jordiorlando/EnLiST-Rover/Eagle/Rover Motor Controller/eagleUp/eagleUp_Rover Motor Controller_bottom_silk.png

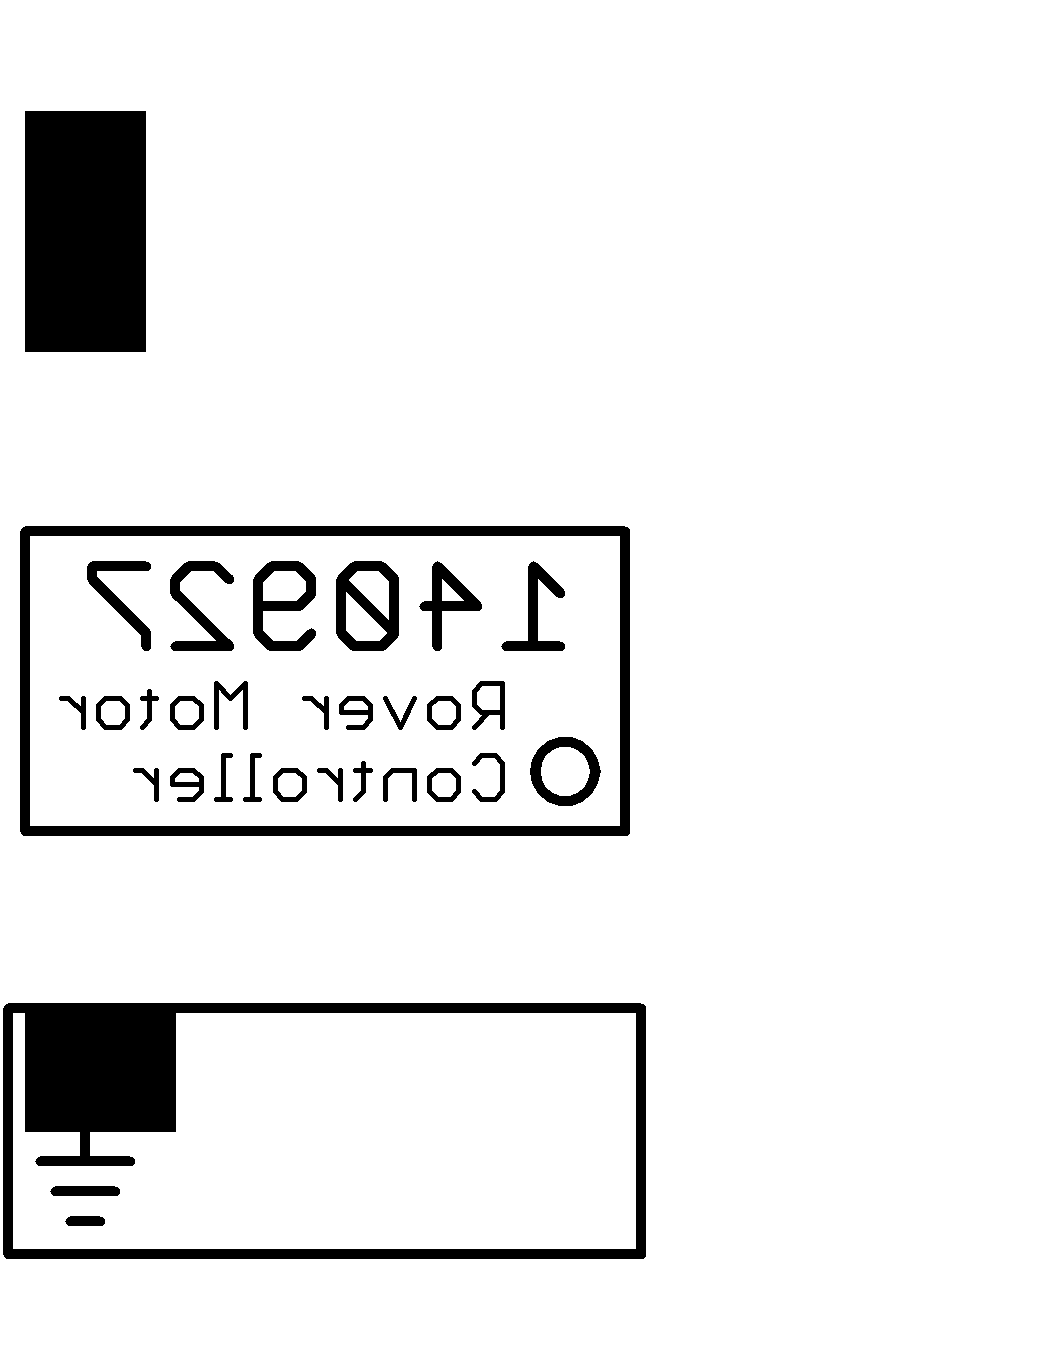
Eagle/Rover Motor Controller/eagleUp/eagleUp_Rover Motor Controller_bottom_silk.png
