jordiorlando/EnLiST-Rover/Eagle/Rover Motor Controller/eagleUp/eagleUp_Rover Motor Controller_outline.png

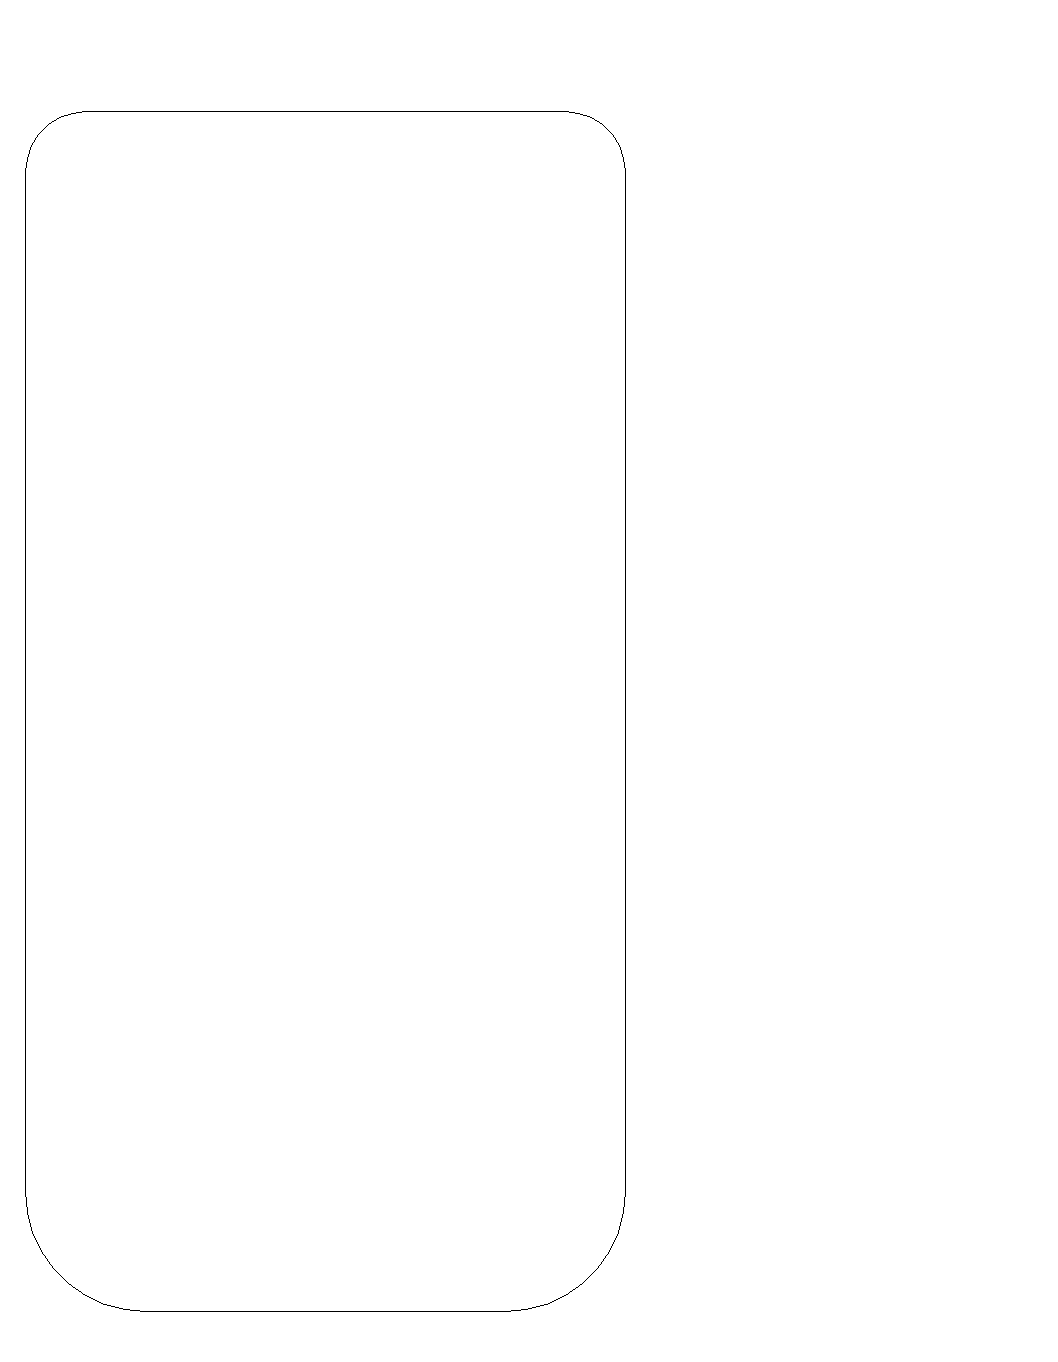
Eagle/Rover Motor Controller/eagleUp/eagleUp_Rover Motor Controller_outline.png
