jordiorlando/EnLiST-Rover/media/photos/15-01-04/IMG_0461.jpg

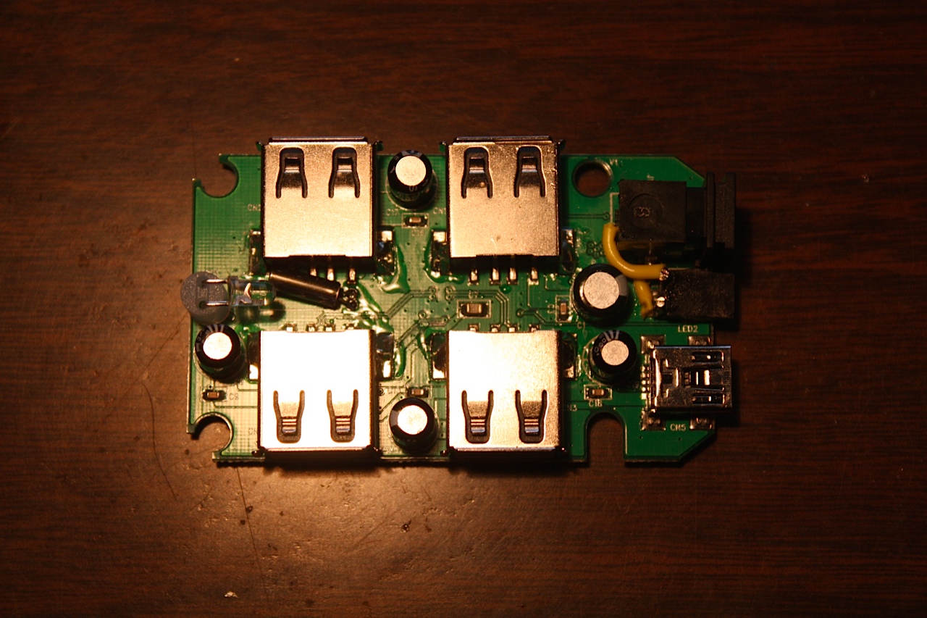
media/photos/15-01-04/IMG_0461.jpg
