jordiorlando/EnLiST-Rover/media/photos/15-01-04/IMG_0467.jpg

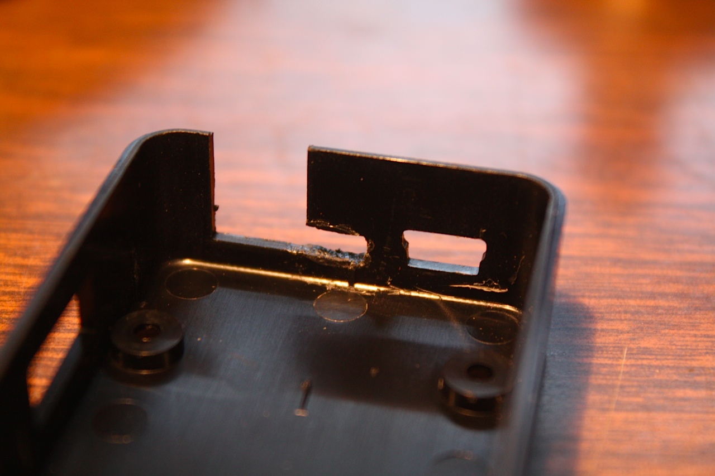
media/photos/15-01-04/IMG_0467.jpg
