jordiorlando/EnLiST-Rover/media/photos/15-01-04/IMG_0475.jpg

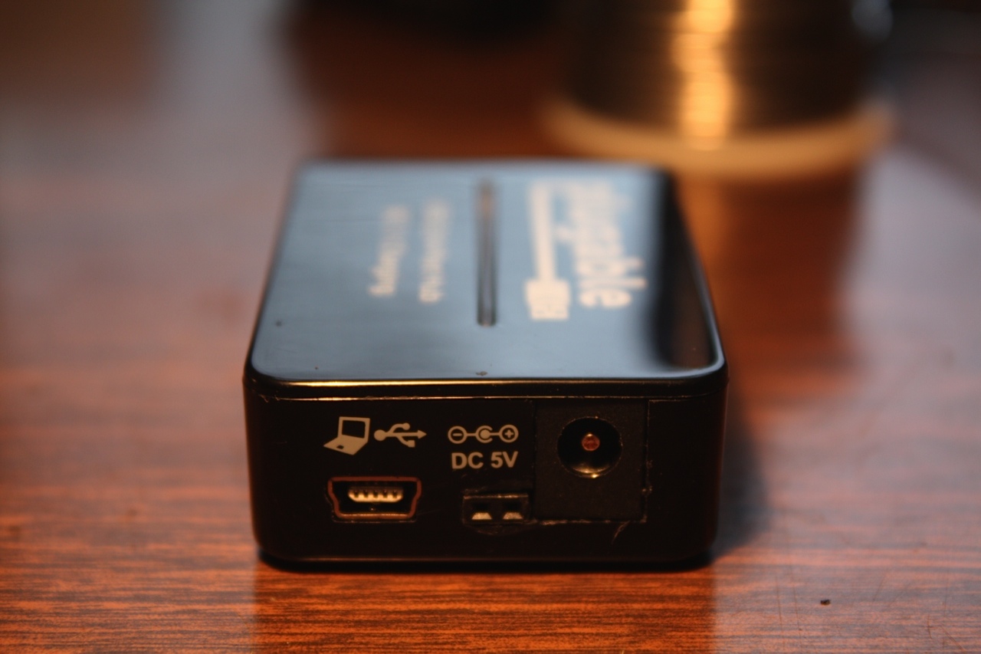
media/photos/15-01-04/IMG_0475.jpg
