jordiorlando/EnLiST-Rover/resources/hardware/Motor Controller Schematic.png

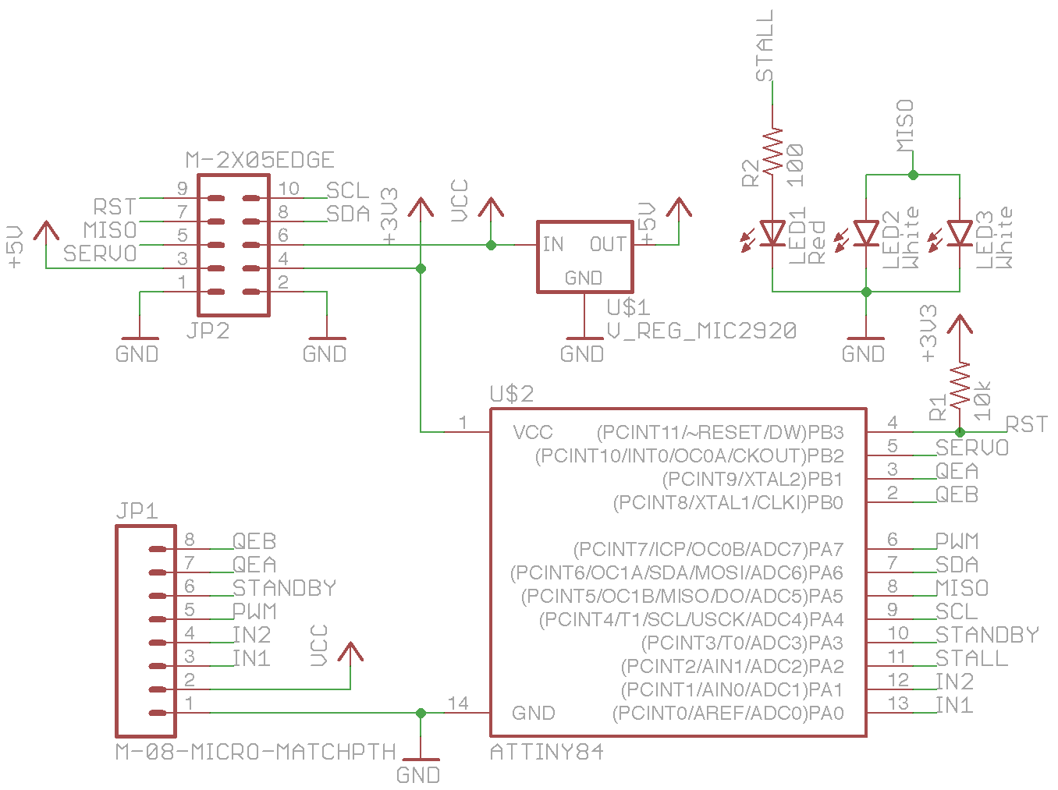
resources/hardware/Motor Controller Schematic.png
