jordiorlando/EnLiST-Rover/resources/Inspiration/Curiosity Rover.jpg

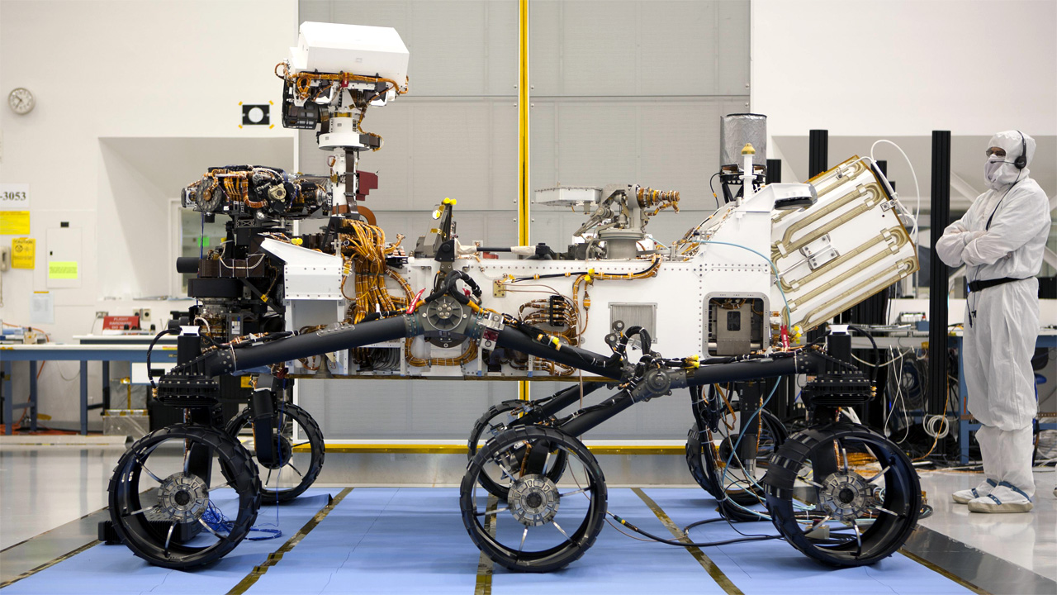
resources/Inspiration/Curiosity Rover.jpg
