jordiorlando/EnLiST-Rover/software/BBB/controllerInput.cpp

#include "controllerInput.h"

controllerInput::controllerInput(tcpSocket & server)
{
    this->server = &server;

    memset(&data, 0, sizeof(data));

    pfd.fd      = this->server->hostfd;
    pfd.events  = POLLIN;
    pfd.revents = 0;
}

void controllerInput::updateValues()
{
    //wait up to 100ms
    poll(&pfd, 1, 100);

    //data ready
    if (pfd.revents & POLLIN)
    {
        ssize_t len;
        unsigned char buf[6];

        //chew up any stale controller data
        while ((len = recv(pfd.fd, buf, 6, MSG_DONTWAIT)) > 0);

        data.square   = (buf[0] >> 0) & 0x1;
        data.cross    = (buf[0] >> 1) & 0x1;
        data.circle   = (buf[0] >> 2) & 0x1;
        data.triangle = (buf[0] >> 3) & 0x1;
        data.l1       = (buf[0] >> 4) & 0x1;
        data.l2       = (buf[0] >> 5) & 0x1;
        data.r1       = (buf[0] >> 6) & 0x1;
        data.r2       = (buf[0] >> 7) & 0x1;

        data.select      = (buf[1] >> 0) & 0x1;
        data.start       = (buf[1] >> 1) & 0x1;
        data.left_stick  = (buf[1] >> 2) & 0x1;
        data.right_stick = (buf[1] >> 3) & 0x1;
        data.d_up        = (buf[1] >> 4) & 0x1;
        data.d_down      = (buf[1] >> 5) & 0x1;
        data.d_left      = (buf[1] >> 6) & 0x1;
        data.d_right     = (buf[1] >> 7) & 0x1;

        data.left_x  = (float)( buf[2] - 0x80 + (1 * (buf[2] < 0x80)) ) / 0x80;
        data.left_y  = (float)( buf[3] - 0x80 + (1 * (buf[3] < 0x80)) ) / 0x80;
        data.right_x = (float)( buf[4] - 0x80 + (1 * (buf[4] < 0x80)) ) / 0x80;
        data.right_y = (float)( buf[5] - 0x80 + (1 * (buf[5] < 0x80)) ) / 0x80;

    }
}
